BrnoMarsRover/Drilling/code/mainBoardProgram/src/DeepSampler/DeepSampler.cpp

 #include "DeepSampler.h"

// ------------------------------------------------------------------ //
//  Public                                                            //
// ------------------------------------------------------------------ //

DeepSampler::DeepSampler(TwoWire& wire, HardwareSerial& debugSerial):
  _wire(wire),
  _debugSerial(debugSerial),
  _stepperEngine(),
  _drillController(wire, debugSerial, _stepperEngine),
  _deepSampleHolder(wire, debugSerial, _stepperEngine)
{
  
}

bool DeepSampler::begin()
{
  _stepperEngine.init();

  if(_drillController.begin() && _deepSampleHolder.begin())
    return true;
  else
    return false;  
}

void DeepSampler::update()
{
  _drillController.update();
  _deepSampleHolder.update();

  switch(_autoState)
  {
    case AutoState::MANUAL:
    {
      break;
    }

    case AutoState::WAITING_FOR_STORAGE_CLEAR:
    {
      if(!_deepSampleHolder.storageIsMoving())
      {
        if (_deepSampleHolder.storageGetCurrentSlot() == StepperPositioner::StoragePosition::Home)
        {
          if(_drillController.autoDrillToDepth(9, 50, _targetDepthMM ) )
          {
            _autoState = AutoState::DRILLING;
          }
          else
          {
            enterError();
          }
        }
        else
        {
          enterError();
        }
      }
      break;
    }
    
    case AutoState::DRILLING:
    {
      if(_drillController.getAutoState() == DrillController::AutoState::DONE)
      {
        _drillController.setManualControl();
        _autoState = AutoState::MOVE_CARRIAGE_TO_STORE;
      }
      if(_drillController.getAutoState() == DrillController::AutoState::ERROR)
      {
        enterError();
      }
      break;
    }

    case AutoState::MOVE_CARRIAGE_TO_STORE:
    {        
      if(_drillController.spiralDepthBelowSensor() < storingPositionTop)
      {
        if(_drillController.setCarriageSpeedMMps(10))
        {
          _autoState = AutoState::MOVING_CARRIAGE_TO_STORE;
        }
        else
        {
          enterError();
        }
      }
      else if(_drillController.spiralDepthBelowSensor() > storingPositionBottom)
      {
        if(_drillController.setCarriageSpeedMMps(-10))
        {
          _autoState = AutoState::MOVING_CARRIAGE_TO_STORE; 
        }
        else
        {
          enterError();
        }
      }
      else
      {
        _autoState = AutoState::MOVING_CARRIAGE_TO_STORE;
      }
      
      break;
    }

    case AutoState::MOVING_CARRIAGE_TO_STORE:
    {
      if(_drillController.spiralDepthBelowSensor() > storingPositionTop && _drillController.spiralDepthBelowSensor() < storingPositionBottom)
      {
        if(_drillController.setCarriageSpeedMMps(0))
        {
          if(_deepSampleHolder.storageMoveToSlot(_divideSlots[_divideSlotIndex]))
          {
            _autoState = AutoState::MOVING_STORAGE; 
          }
          else
          {
            enterError();
          }
        }
        else
        {
          enterError();
        }
      }
      break;
    }
    
    case AutoState::MOVING_STORAGE:
    {
      if(!_deepSampleHolder.storageIsMoving())
      {
        if(_deepSampleHolder.storageGetCurrentSlot() == _divideSlots[_divideSlotIndex])
        {
          if(_drillController.setSpiralRPM(_storingRPM))
          {
            _storingStartTimeMS = millis();
            _autoState = AutoState::STORING;
          }
          else
          {
            enterError();
          }
        }
        else
        {
          enterError();
        }
      }

      break;
    }
    
    case AutoState::STORING:
    {
      if(millis() - _storingStartTimeMS > _storingDurationMS)
      {
        if(_drillController.setSpiralRPM(0))
        {
          _divideSlotIndex++;
          if(_divideSlotIndex < 3)
          {
            if(_deepSampleHolder.storageMoveToSlot(_divideSlots[_divideSlotIndex]))
            {
              _autoState = AutoState::MOVING_STORAGE;
            }
            else
            {
              enterError();
            }
          }
          else
          {
            if(_deepSampleHolder.startAutoWeighing())
            {
              _autoState = AutoState::WEIGHING;
            }
            else {enterError();}
          }
        }
        else
        {
          enterError();
        }
      }
      break;
    }
    
    case AutoState::WEIGHING:
    {
      if(_deepSampleHolder.getAutoState() == DeepSampleHolder::AutoState::DONE)
      {
        _deepSampleHolder.setManualControl();

        if(_drillController.setCarriageSpeedMMps(-10.0) && _deepSampleHolder.storageMoveToSlot(StepperPositioner::StoragePosition::Home))
        {
          _autoState = AutoState::MOVING_UP;
        }
        else
        {
          enterError();
        }
      }
      if(_deepSampleHolder.getAutoState() == DeepSampleHolder::AutoState::ERROR)
      {
        enterError();
      }
      break;
    }
    
    case AutoState::MOVING_UP:
    {
      if(_drillController.getCarriageDepthMM() < 1.0 && _deepSampleHolder.storageGetCurrentSlot() == StepperPositioner::StoragePosition::Home)
      {
        _autoState = AutoState::DONE;
      }
      break;
    }
  
    case AutoState::DONE:
    {
      break;
    }
    
    case AutoState::ERROR:
    {

      break;
    }
  }
}

// Integrated carriage/spiral motor control
DeepSampler::AutoState DeepSampler::getAutoState() {return _autoState; }
DrillController::AutoState DeepSampler::getDrillControllerState() {return _drillController.getAutoState(); }
DeepSampleHolder::AutoState DeepSampler::getDeepSampleHolderState() {return _deepSampleHolder.getAutoState(); }

bool DeepSampler::setManualControl()
{
  _autoState = AutoState::MANUAL;
  _deepSampleHolder.setManualControl();
  _drillController.setManualControl();
  return true;
}
bool DeepSampler::startDistFromSurfaceMeasure() {return _drillController.startDistFromSurfaceMeasure(); }
float DeepSampler::getDistFromSurfaceMM() {return _drillController.getDistFromSurfaceMM(); }


bool DeepSampler::autoDrillStoreWeigh(float targetDepthMM)
{
  if(_autoState == AutoState::MANUAL && _drillController.isDepthCalibrated())
  {
    if(_deepSampleHolder.storageMoveToSlot(StepperPositioner::StoragePosition::Home))
    {
      _divideSlotIndex = 0;
      _targetDepthMM = targetDepthMM;
      _autoState = AutoState::WAITING_FOR_STORAGE_CLEAR;
      return true;
    }
    else{ return false; }
  }
  else { return false; }
}

bool DeepSampler::autoStoreWeigh()
{
  if(_autoState == AutoState::MANUAL && _drillController.isDepthCalibrated())
  {
    _divideSlotIndex = 0;
    _autoState = AutoState::MOVE_CARRIAGE_TO_STORE;
    return true;
  }
  else {return false;}
}

// Low level carriage/vertical drive control
bool DeepSampler::setCarriageSpeedMMps(float MMps)
{
  return _drillController.setCarriageSpeedMMps(MMps);
}

float DeepSampler::getCarriageSpeedMMps() const { return _drillController.getCarriageSpeedMMps(); }
float DeepSampler::getCarriageDepthMM() const { return _drillController.getCarriageDepthMM(); }
float DeepSampler::getVerticalStepperCurrentA() const { return _drillController.getVerticalStepperCurrentA(); }
bool DeepSampler::currentSensorIsConnected() const {return _drillController.currentSensorIsConnected(); }

// Low level spiral motor control
bool DeepSampler::setSpiralRPM(float rpm) { return _drillController.setSpiralRPM(rpm); }
CubeMarsData DeepSampler::getSpiralMotorData() { return _drillController.getSpiralMotorData(); }

//Storage control
bool DeepSampler::setCalibration0() { return _deepSampleHolder.setCalibration0(); }
bool DeepSampler::setCalibrationX(float weightX) { return _deepSampleHolder.setCalibrationX(weightX); }

bool DeepSampler::getResultReady() { return _deepSampleHolder.getResultReady(); }
WeightResult DeepSampler::getLastWeight() { return _deepSampleHolder.getLastWeight(); }
float DeepSampler::getLastTemp() { return _deepSampleHolder.getLastTemp(); }

bool DeepSampler::requestMeasure() { return _deepSampleHolder.requestMeasure(); }
bool DeepSampler::requestTemp() { return _deepSampleHolder.requestTemp(); }

bool DeepSampler::storageMoveToSlot(StepperPositioner::StoragePosition position)
{
  _deepSampleHolder.storageMoveToSlot(position);
  return true;
}

bool DeepSampler::storageUnlock()
{
  _deepSampleHolder.storageUnlock();
  return true;
}

bool DeepSampler::storageSetHoldMode(bool hold)
{
  _deepSampleHolder.storageSetHoldMode(hold);
  return true;
}

uint16_t DeepSampler::storageGetCurrentAngle()  const {return _deepSampleHolder.storageGetCurrentAngle(); }

// Connection checks
bool DeepSampler::verticalEncoderConnected() {return _drillController.encoderConnected();}
bool DeepSampler::verticalStepperConnected() {return _drillController.stepperConnected();}
bool DeepSampler::spiralMotorConnected() {return _drillController.spiralMotorConnected();}
bool DeepSampler::heightSensorConnected() {return _drillController.heightSensorConnected();}
bool DeepSampler::getAdcConnected() {return _deepSampleHolder.getAdcConnected();}
bool DeepSampler::deepSampleEncoderConnected() {return _deepSampleHolder.storageEncoderConnected(); }
bool DeepSampler::deepSampleStepperConnected() {return _deepSampleHolder.storageStepperConnected(); }

void DeepSampler::enterError()
{
  _drillController.setManualControl();
  _drillController.setCarriageSpeedMMps(0);
  _drillController.setSpiralRPM(0);
  _deepSampleHolder.setManualControl();
  _deepSampleHolder.storageStop();
  _autoState = AutoState::ERROR;
}
