BrnoMarsRover/Drilling/code/pcInterface/protocol.py

"""
protocol.py

Handles building and parsing of UART messages according to the drill protocol spec.

Message format:
  0x02 | length | payload... | checksum | 0x03

Checksum: sum complement of payload bytes (0x100 - (sum(payload) & 0xFF)) & 0xFF

Two-step commands (trigger then poll):
  WEIGH_DEEP        -> GET_WEIGHT_DEEP
  WEIGH_SURFACE     -> GET_WEIGHT_SURFACE
  START_DEV_CHECK   -> GET_DEVICE_STATUS
  MEASURE_HEIGHT    -> GET_HEIGHT
"""

import struct

# --- Message framing bytes ---
STX = 0x02
ETX = 0x03

# --- Command codes ---
CMD_RESTART            = 0x01
CMD_STATE              = 0x02
CMD_CALIBRATE_HEIGHT   = 0x03
CMD_START_DEV_CHECK    = 0x04
CMD_GET_DEVICE_STATUS  = 0x05
CMD_DRILL_SPEED        = 0x20
CMD_VERTICAL_SPEED     = 0x21
CMD_STORAGE_POSITION   = 0x22
CMD_MEASURE_HEIGHT     = 0x23
CMD_GET_HEIGHT         = 0x24
CMD_WEIGH_DEEP         = 0x40
CMD_WEIGH_SURFACE      = 0x41
CMD_GET_WEIGHT_DEEP    = 0x42
CMD_GET_WEIGHT_SURFACE = 0x43
CMD_CALIBRATE_0_DEEP   = 0x44
CMD_CALIBRATE_X_DEEP   = 0x45
CMD_CALIBRATE_0_SURFACE= 0x46
CMD_CALIBRATE_X_SURFACE= 0x47
CMD_ROCK_OPEN          = 0x50
CMD_ROCK_CLOSE         = 0x51
CMD_SAND_OPEN          = 0x52
CMD_SAND_CLOSE         = 0x53
CMD_SET_HOLD_MODE      = 0x54
CMD_CLEAR_HOLD_MODE    = 0x55
CMD_STOP_AUTO          = 0x60
CMD_DRILL_AUTO         = 0x61
CMD_STORE_AUTO         = 0x62


# --- Autonomy state codes ---
# Three independent state machines, each reported as its own uint8 in the
# STATE response. Codes and meanings per protocol spec.

DEEP_SAMPLER_STATE_CODES = {
    0x00: "MANUAL",
    0x01: "WAITING_FOR_STORAGE_CLEAR",
    0x02: "DRILLING",
    0x03: "MOVE_CARRIAGE_TO_STORE",
    0x04: "MOVING_CARRIAGE_TO_STORE",
    0x05: "MOVING_STORAGE",
    0x06: "STORING",
    0x07: "WEIGHING",
    0x08: "MOVING_UP",
    0xFE: "DONE",
    0xFF: "ERROR",
}

DRILL_CONTROLLER_STATE_CODES = {
    0x00: "MANUAL",
    0x01: "WAITING_FOR_HEIGHT",
    0x02: "MOVING_DOWN",
    0x03: "DRILLING",
    0xFE: "DONE",
    0xFF: "ERROR",
}

DEEP_SAMPLE_HOLDER_STATE_CODES = {
    0x00: "MANUAL",
    0x01: "STORAGE_MOVING",
    0x02: "WAITING_FOR_SETTLE",
    0x03: "WEIGHING",
    0xFE: "DONE",
    0xFF: "ERROR",
}

# --- Device status bit order (LSB first) ---
DEVICE_NAMES = [
    "Vertical drive stepper driver",   # bit 0
    "Vertical drive encoder",          # bit 1
    "Vertical drive current sensor",   # bit 2
    "Spiral motor",                    # bit 3
    "Height sensor",                   # bit 4
    "Deep storage stepper driver",     # bit 5
    "Deep storage encoder",            # bit 6
    "Deep sample ADC",                 # bit 7
    "Surface sample ADC",              # bit 8
]


def checksum(payload: bytes) -> int:
    """Sum complement checksum over payload bytes."""
    return (0x100 - (sum(payload) & 0xFF)) & 0xFF


def build_message(payload: bytes) -> bytes:
    """Wrap a payload in the full message frame."""
    cs = checksum(payload)
    return bytes([STX, len(payload)]) + payload + bytes([cs, ETX])


def build_command(code: int, argument: bytes = b"") -> bytes:
    """Build a complete framed message for a given command code and optional argument."""
    payload = bytes([code]) + argument
    return build_message(payload)


# --- Convenience command builders ---

def cmd_restart():
    return build_command(CMD_RESTART)

def cmd_state():
    return build_command(CMD_STATE)

def cmd_drill_auto(depth_cm: int):
    return build_command(CMD_DRILL_AUTO, struct.pack("B", depth_cm))

def cmd_stop_auto():
    return build_command(CMD_STOP_AUTO)

def cmd_calibrate_height():
    return build_command(CMD_CALIBRATE_HEIGHT)

def cmd_start_dev_check():
    return build_command(CMD_START_DEV_CHECK)

def cmd_get_device_status():
    return build_command(CMD_GET_DEVICE_STATUS)

def cmd_store_auto():
    return build_command(CMD_STORE_AUTO)

def cmd_drill_speed(rpm: int):
    return build_command(CMD_DRILL_SPEED, struct.pack(">h", rpm))

def cmd_vertical_speed(mm_per_s: float):
    # convert float mm/s to int8 (units of 0.1 mm/s)
    raw = int(round(mm_per_s * 10))
    return build_command(CMD_VERTICAL_SPEED, struct.pack("b", raw))

def cmd_storage_position(position: int):
    return build_command(CMD_STORAGE_POSITION, struct.pack("B", position))

def cmd_measure_height():
    return build_command(CMD_MEASURE_HEIGHT)

def cmd_get_height():
    return build_command(CMD_GET_HEIGHT)

def cmd_weigh_deep():
    return build_command(CMD_WEIGH_DEEP)

def cmd_weigh_surface():
    return build_command(CMD_WEIGH_SURFACE)

def cmd_get_weight_deep():
    return build_command(CMD_GET_WEIGHT_DEEP)

def cmd_get_weight_surface():
    return build_command(CMD_GET_WEIGHT_SURFACE)

def cmd_calibrate_0_deep():
    return build_command(CMD_CALIBRATE_0_DEEP)

def cmd_calibrate_x_deep(weight_g: float):
    return build_command(CMD_CALIBRATE_X_DEEP, struct.pack(">f", weight_g))

def cmd_calibrate_0_surface():
    return build_command(CMD_CALIBRATE_0_SURFACE)

def cmd_calibrate_x_surface(weight_g: float):
    return build_command(CMD_CALIBRATE_X_SURFACE, struct.pack(">f", weight_g))

def cmd_set_hold_mode():
    return build_command(CMD_SET_HOLD_MODE)

def cmd_clear_hold_mode():
    return build_command(CMD_CLEAR_HOLD_MODE)

def cmd_rock_open():
    return build_command(CMD_ROCK_OPEN)

def cmd_rock_close():
    return build_command(CMD_ROCK_CLOSE)

def cmd_sand_open():
    return build_command(CMD_SAND_OPEN)

def cmd_sand_close():
    return build_command(CMD_SAND_CLOSE)


# --- Response parsing ---

def parse_response(data: bytes):
    """
    Parse a complete raw message (including framing bytes).
    Returns a dict with parsed fields, or None if the message is invalid.

    Possible keys in the returned dict:
      'code'          : int   — the echoed command code (or 0 for NACK)
      'nack'          : bool  — True if the drill refused the command
      'state'         : dict  — present if code == CMD_STATE. Includes
                                 separate deep_sampler_state,
                                 drill_controller_state, and
                                 deep_sample_holder_state fields (each
                                 with a matching *_str name).
      'weight'        : float — present if code == CMD_GET_WEIGHT_DEEP/SURFACE
      'adc_raw'       : int   — raw ADC value, present alongside 'weight'
      'height_mm'     : int   — present if code == CMD_GET_HEIGHT
      'device_status' : list  — present if code == CMD_GET_DEVICE_STATUS
    """
    if len(data) < 5:
        return None
    if data[0] != STX or data[-1] != ETX:
        return None

    payload_length = data[1]
    payload = data[2 : 2 + payload_length]
    received_checksum = data[2 + payload_length]

    if len(payload) != payload_length:
        return None
    if checksum(payload) != received_checksum:
        return None

    code = payload[0]

    if code == 0x00:
        return {"code": 0, "nack": True}

    result = {"code": code, "nack": False}

    if code == CMD_STATE and len(payload) >= 19:
        # int16 height_mm, int8 vert_speed, uint8 stepper_current,
        # int16 rpm, int16 motor_winding_current, int16 motor_current_draw,
        # int16 motor_torque, uint8 temp, uint16 tray_angle,
        # uint8 deep_sampler_state, uint8 drill_controller_state,
        # uint8 deep_sample_holder_state
        (height, vert_speed, current, rpm,
         motor_winding_current, motor_current_draw, motor_torque,
         temp, tray_angle, deep_sampler_state, drill_controller_state,
         deep_sample_holder_state) = \
            struct.unpack_from(">hbBhhhhBHBBB", payload, 1)
        result["state"] = {
            "height_mm":               height,
            "vert_speed":              vert_speed / 10.0,
            "current_a":               current / 100.0,
            "rpm":                     rpm,
            "motor_winding_current_a": motor_winding_current / 100.0,
            "motor_current_draw_a":    motor_current_draw / 100.0,
            "motor_torque_nm":         motor_torque / 100.0,
            "temp_c":                  temp,
            "tray_angle":              tray_angle,
            "deep_sampler_state":      deep_sampler_state,
            "deep_sampler_state_str": DEEP_SAMPLER_STATE_CODES.get(
                deep_sampler_state, f"Unknown (0x{deep_sampler_state:02X})"),
            "drill_controller_state":  drill_controller_state,
            "drill_controller_state_str": DRILL_CONTROLLER_STATE_CODES.get(
                drill_controller_state, f"Unknown (0x{drill_controller_state:02X})"),
            "deep_sample_holder_state": deep_sample_holder_state,
            "deep_sample_holder_state_str": DEEP_SAMPLE_HOLDER_STATE_CODES.get(
                deep_sample_holder_state, f"Unknown (0x{deep_sample_holder_state:02X})"),
        }

    elif code in (CMD_GET_WEIGHT_DEEP, CMD_GET_WEIGHT_SURFACE) and len(payload) >= 9:
        weight, adc_raw = struct.unpack_from(">fI", payload, 1)
        result["weight"]  = weight
        result["adc_raw"] = adc_raw

    elif code == CMD_GET_HEIGHT and len(payload) >= 3:
        result["height_mm"] = struct.unpack_from(">H", payload, 1)[0]

    elif code == CMD_GET_DEVICE_STATUS and len(payload) >= 3:
        status_bits = struct.unpack_from(">H", payload, 1)[0]
        devices = []
        for i, name in enumerate(DEVICE_NAMES):
            devices.append({
                "name": name,
                "ok":   bool(status_bits & (1 << i)),
            })
        result["device_status"] = devices

    return result
