BrnoMarsRover/Drilling/code/pcInterface/gui.py

"""
gui.py

Tkinter GUI for the drilling HMI.
All communication goes through the CommWorker — the GUI never touches the
serial port or UDP socket directly. CommWorker supports two transports,
switchable from the Connection bar: direct USB serial to the ESP32, or a
localhost UDP link to the main rover communication app.

Layout (4 columns, 2 content rows):
  Col 0: Drill status + Manual controls
  Col 1 row 1: Auto drilling + Height measurement
  Col 1 row 2: Sample handling
  Col 2 row 1: Device status
  Col 2 row 2: Calibration
  Col 3 rows 1-2: Log
"""

import tkinter as tk
from tkinter import ttk, messagebox
import serial.tools.list_ports
import protocol
import time

POLL_INTERVAL_MS       = 100
STATE_POLL_INTERVAL_MS = 500

# Localhost UDP ports, per communicationProtocol.md:
# this app sends to the main rover app on 5610 and receives replies on 5611.
DEFAULT_UDP_SEND_PORT   = 5610
DEFAULT_UDP_LISTEN_PORT = 5611


class App(tk.Tk):
    def __init__(self, worker):
        super().__init__()
        self.worker = worker
        self.title("Drilling HMI")
        self.resizable(True, True)

        self._build_connection_bar()
        self._build_columns()
        self._build_status_panel()
        self._build_manual_controls()
        self._build_height_panel()
        self._build_autonomy_controls()
        self._build_sample_controls()
        self._build_device_status_panel()
        self._build_weight_panel()
        self._build_calibration_panel()
        self._build_log()

        self._configure_resizing()

        self._poll_rx()
        self._poll_state()

    def _build_columns(self):
        """
        One container per column. Panels are packed vertically inside their
        column, so a tall panel in one column no longer forces gaps between
        the panels of its neighbours (which a shared grid row would).
        """
        self.columns = []
        for i in range(4):
            container = ttk.Frame(self)
            container.grid(row=1, column=i, sticky="nsew")
            self.columns.append(container)

    def _configure_resizing(self):
        """
        Let the window be resized. The log column takes the extra width and
        the two content rows share the extra height; the fixed-content
        columns keep their natural size. The minimum size is locked to the
        laid-out size so nothing can be clipped by shrinking the window.
        """
        # Column 3 (log) absorbs horizontal growth; the other columns hold
        # fixed-size controls and keep their natural width.
        self.columnconfigure(3, weight=1)
        # The single content row absorbs vertical growth;
        # row 0 (connection bar) stays fixed.
        self.rowconfigure(1, weight=1)

        self.update_idletasks()
        self.minsize(self.winfo_reqwidth(), self.winfo_reqheight())

    # ------------------------------------------------------------------ #
    #  Connection bar                                                      #
    # ------------------------------------------------------------------ #

    def _build_connection_bar(self):
        frame = ttk.LabelFrame(self, text="Connection")
        frame.grid(row=0, column=0, columnspan=4, padx=8, pady=6, sticky="ew")

        # --- Transport mode selector ---
        ttk.Label(frame, text="Mode:").grid(row=0, column=0, padx=4, pady=4)
        self.conn_mode_var = tk.StringVar(value="serial")
        self.serial_radio = ttk.Radiobutton(
            frame, text="USB Serial", variable=self.conn_mode_var,
            value="serial", command=self._on_mode_change)
        self.serial_radio.grid(row=0, column=1, padx=(4, 0), pady=4, sticky="w")
        self.udp_radio = ttk.Radiobutton(
            frame, text="UDP (localhost)", variable=self.conn_mode_var,
            value="udp", command=self._on_mode_change)
        self.udp_radio.grid(row=0, column=2, padx=(4, 12), pady=4, sticky="w")

        # --- Serial-specific controls (shown when Mode == USB Serial) ---
        self.serial_frame = ttk.Frame(frame)
        self.serial_frame.grid(row=0, column=3, padx=4, pady=4, sticky="w")
        ttk.Label(self.serial_frame, text="COM port:").pack(side="left")
        self.port_var = tk.StringVar()
        self.port_combo = ttk.Combobox(
            self.serial_frame, textvariable=self.port_var, width=12, state="readonly")
        self.port_combo.pack(side="left", padx=4)
        self.refresh_btn = ttk.Button(self.serial_frame, text="Refresh", command=self._refresh_ports)
        self.refresh_btn.pack(side="left")

        # --- UDP-specific controls (shown when Mode == UDP) ---
        self.udp_frame = ttk.Frame(frame)
        self.udp_frame.grid(row=0, column=3, padx=4, pady=4, sticky="w")
        ttk.Label(self.udp_frame, text="Listen port (from main app):").pack(side="left")
        self.udp_local_port_var = tk.StringVar(value=str(DEFAULT_UDP_LISTEN_PORT))
        ttk.Entry(self.udp_frame, textvariable=self.udp_local_port_var, width=6).pack(
            side="left", padx=(4, 12))
        ttk.Label(self.udp_frame, text="Send port (to main app):").pack(side="left")
        self.udp_remote_port_var = tk.StringVar(value=str(DEFAULT_UDP_SEND_PORT))
        ttk.Entry(self.udp_frame, textvariable=self.udp_remote_port_var, width=6).pack(
            side="left", padx=4)

        self.connect_btn = ttk.Button(frame, text="Connect", command=self._toggle_connection)
        self.connect_btn.grid(row=0, column=4, padx=4)
        self.conn_status = ttk.Label(frame, text="Disconnected", foreground="red")
        self.conn_status.grid(row=0, column=5, padx=8)

        self._refresh_ports()
        self._on_mode_change()

    def _on_mode_change(self):
        """Show the controls relevant to the selected transport mode."""
        if self.conn_mode_var.get() == "serial":
            self.udp_frame.grid_remove()
            self.serial_frame.grid()
        else:
            self.serial_frame.grid_remove()
            self.udp_frame.grid()

    def _set_mode_controls_enabled(self, enabled: bool):
        """Lock the mode switch and its fields while connected."""
        state = "normal" if enabled else "disabled"
        combo_state = "readonly" if enabled else "disabled"
        self.serial_radio.config(state=state)
        self.udp_radio.config(state=state)
        self.port_combo.config(state=combo_state)
        self.refresh_btn.config(state=state)
        for child in self.udp_frame.winfo_children():
            if isinstance(child, ttk.Entry):
                child.config(state=state)

    def _refresh_ports(self):
        ports = [p.device for p in serial.tools.list_ports.comports()]
        self.port_combo["values"] = ports
        if ports:
            self.port_combo.current(0)

    def _toggle_connection(self):
        if self.worker.is_connected():
            self.worker.disconnect()
            self.connect_btn.config(text="Connect")
            self.conn_status.config(text="Disconnected", foreground="red")
            self._set_mode_controls_enabled(True)
            self._log("Disconnected.")
            return

        mode = self.conn_mode_var.get()

        if mode == "serial":
            port = self.port_var.get()
            if not port:
                messagebox.showerror("Error", "No COM port selected.")
                return
            ok = self.worker.connect_serial(port)
            description = port
        else:
            try:
                local_port = int(self.udp_local_port_var.get())
                remote_port = int(self.udp_remote_port_var.get())
            except ValueError:
                messagebox.showerror("Error", "UDP ports must be numbers.")
                return
            if not (0 < local_port <= 65535 and 0 < remote_port <= 65535):
                messagebox.showerror("Error", "UDP ports must be between 1 and 65535.")
                return
            if local_port == remote_port:
                messagebox.showerror("Error", "Listen port and send port must be different.")
                return
            ok = self.worker.connect_udp(local_port, remote_port)
            description = f"UDP — listen {local_port} / send {remote_port}"

        if ok:
            self.connect_btn.config(text="Disconnect")
            self.conn_status.config(text=f"Connected ({description})", foreground="green")
            self._set_mode_controls_enabled(False)
            self._log(f"Connected: {description}.")
        else:
            self._log(f"Failed to connect: {description}.")

    # ------------------------------------------------------------------ #
    #  Status panel (STATE response)  — column 0                          #
    # ------------------------------------------------------------------ #

    def _build_status_panel(self):
        frame = ttk.LabelFrame(self.columns[0], text="Drill status  (auto-refreshed)")
        frame.pack(fill="x", padx=8, pady=6)

        # Numeric readouts — a narrow fixed width is enough for every value
        # these ever hold, and it keeps the left column compact.
        labels = [
            ("Carriage depth",         "carriage_depth_var",  "mm"),
            ("Depth under rover",      "depth_under_rover_var","mm"),
            ("Depth under surface",    "depth_under_surface_var","mm"),
            ("Vertical speed",         "vert_speed_actual_var","mm/s"),
            ("Stepper current",        "current_var",         "A"),
            ("Motor speed",            "rpm_var",             "RPM"),
            ("Motor winding current",  "motor_winding_current_var", "A"),
            ("Motor current draw",     "motor_current_draw_var",    "A"),
            ("Motor torque",           "motor_torque_var",    "Nm"),
            ("Motor temp",             "temp_var",            "°C"),
            ("Tray angle",             "tray_var",            "°"),
        ]

        for i, (label, attr, unit) in enumerate(labels):
            ttk.Label(frame, text=label + ":").grid(row=i, column=0, sticky="w", padx=6, pady=2)
            var = tk.StringVar(value="—")
            setattr(self, attr, var)
            ttk.Label(frame, textvariable=var, width=10, anchor="w").grid(
                row=i, column=1, sticky="w", padx=4)
            if unit:
                ttk.Label(frame, text=unit).grid(row=i, column=2, sticky="w", padx=(0, 6))

        ttk.Separator(frame, orient="horizontal").grid(
            row=len(labels), column=0, columnspan=3, sticky="ew", pady=4)

        # State names are long (e.g. MOVING_CARRIAGE_TO_STORE). Wrapping them
        # instead of reserving a wide column keeps the text fully readable
        # without stretching the panel.
        states = [
            ("DeepSampler",      "deep_sampler_state_var"),
            ("DrillController",  "drill_controller_state_var"),
            ("DeepSampleHolder", "deep_sample_holder_state_var"),
        ]
        for j, (label, attr) in enumerate(states):
            row = len(labels) + 1 + j
            ttk.Label(frame, text=label + ":").grid(row=row, column=0, sticky="nw", padx=6, pady=2)
            var = tk.StringVar(value="—")
            setattr(self, attr, var)
            ttk.Label(frame, textvariable=var, wraplength=110,
                      justify="left", anchor="w").grid(
                row=row, column=1, columnspan=2, sticky="w", padx=4)

    # ------------------------------------------------------------------ #
    #  Manual controls — column 0                                          #
    # ------------------------------------------------------------------ #

    def _build_manual_controls(self):
        frame = ttk.LabelFrame(self.columns[0], text="Manual controls")
        frame.pack(fill="x", padx=8, pady=6)

        ttk.Label(frame, text="Drill speed (RPM):").grid(row=0, column=0, sticky="w", padx=6, pady=3)
        self.drill_speed_var = tk.StringVar(value="0")
        ttk.Entry(frame, textvariable=self.drill_speed_var, width=8).grid(row=0, column=1, padx=4)
        ttk.Button(frame, text="Set", width=4, command=self._set_drill_speed).grid(
            row=0, column=2, padx=4)
        ttk.Button(frame, text="Stop", width=5, command=self._stop_drill_speed).grid(
            row=0, column=3, padx=(0, 6))

        ttk.Label(frame, text="Vertical speed (mm/s):").grid(row=1, column=0, sticky="w", padx=6, pady=3)
        self.vert_speed_request_var = tk.StringVar(value="0")
        ttk.Entry(frame, textvariable=self.vert_speed_request_var, width=8).grid(row=1, column=1, padx=4)
        ttk.Button(frame, text="Set", width=4, command=self._set_vertical_speed).grid(
            row=1, column=2, padx=4)
        ttk.Button(frame, text="Stop", width=5, command=self._stop_vertical_speed).grid(
            row=1, column=3, padx=(0, 6))

        ttk.Label(frame, text="Storage position:").grid(row=2, column=0, sticky="w", padx=6, pady=3)
        self.storage_pos_var = tk.StringVar(value="0")
        ttk.Entry(frame, textvariable=self.storage_pos_var, width=8).grid(row=2, column=1, padx=4)
        ttk.Button(frame, text="Set", width=4, command=self._set_storage_position).grid(
            row=2, column=2, padx=4)

        ttk.Separator(frame, orient="horizontal").grid(
            row=3, column=0, columnspan=4, sticky="ew", pady=6)

        ttk.Button(frame, text="Calibrate carriage depth", command=self._calibrate_height).grid(
            row=4, column=0, columnspan=4, sticky="ew", padx=6, pady=2)
        ttk.Button(frame, text="RESTART", command=self._restart).grid(
            row=5, column=0, columnspan=4, sticky="ew", padx=6, pady=2)

    # ------------------------------------------------------------------ #
    #  Automatic drilling — column 1                                       #
    # ------------------------------------------------------------------ #

    def _build_height_panel(self):
        frame = ttk.LabelFrame(self.columns[1], text="Height measurement")
        frame.pack(fill="x", padx=8, pady=6)

        ttk.Label(frame, text="Height above ground:").grid(
            row=0, column=0, sticky="w", padx=6, pady=2)
        self.height_above_ground_var = tk.StringVar(value="—")
        ttk.Label(frame, textvariable=self.height_above_ground_var, width=8, anchor="w").grid(
            row=0, column=1, sticky="w", padx=4)
        ttk.Label(frame, text="mm").grid(row=0, column=2, sticky="w", padx=(0, 6))

        ttk.Button(frame, text="Measure height above ground", command=self._measure_height).grid(
            row=1, column=0, columnspan=3, sticky="ew", padx=6, pady=2)
        ttk.Button(frame, text="Get height above ground", command=self._get_height).grid(
            row=2, column=0, columnspan=3, sticky="ew", padx=6, pady=(2, 6))

    # ------------------------------------------------------------------ #
    #  Autonomy — column 1                                                 #
    # ------------------------------------------------------------------ #

    def _build_autonomy_controls(self):
        frame = ttk.LabelFrame(self.columns[1], text="Autonomy")
        frame.pack(fill="x", padx=8, pady=6)

        ttk.Label(frame, text="Target depth (cm):").grid(row=0, column=0, sticky="w", padx=6, pady=3)
        self.drill_depth_var = tk.StringVar(value="10")
        ttk.Entry(frame, textvariable=self.drill_depth_var, width=8).grid(
            row=0, column=1, sticky="w", padx=4)

        ttk.Button(frame, text="Start auto drill", command=self._drill_auto).grid(
            row=1, column=0, columnspan=2, sticky="ew", padx=6, pady=4)
        ttk.Button(frame, text="Start auto store", command=self._store_auto).grid(
            row=2, column=0, columnspan=2, sticky="ew", padx=6, pady=2)

        ttk.Separator(frame, orient="horizontal").grid(
            row=3, column=0, columnspan=2, sticky="ew", pady=6)

        ttk.Button(frame, text="Stop auto", command=self._stop_auto).grid(
            row=4, column=0, columnspan=2, sticky="ew", padx=6, pady=(2, 6))

    # ------------------------------------------------------------------ #
    #  Sample handling — column 1                                          #
    # ------------------------------------------------------------------ #

    def _build_sample_controls(self):
        frame = ttk.LabelFrame(self.columns[1], text="Sample handling")
        frame.pack(fill="x", padx=8, pady=6)

        # Two columns: the action and its matching counterpart side by side.
        rows = [
            ("Weigh deep",    self._weigh_deep,    "Get deep",    self._get_weight_deep),
            ("Weigh surface", self._weigh_surface, "Get surface", self._get_weight_surface),
            ("Rock open",     self._rock_open,     "Rock close",  self._rock_close),
            ("Sand open",     self._sand_open,     "Sand close",  self._sand_close),
            ("Set hold",      self._set_hold_mode, "Clear hold",  self._clear_hold_mode),
        ]
        for i, (left_label, left_cmd, right_label, right_cmd) in enumerate(rows):
            ttk.Button(frame, text=left_label, command=left_cmd).grid(
                row=i, column=0, sticky="ew", padx=(6, 2), pady=2)
            ttk.Button(frame, text=right_label, command=right_cmd).grid(
                row=i, column=1, sticky="ew", padx=(2, 6), pady=2)

        frame.columnconfigure(0, weight=1, uniform="sample")
        frame.columnconfigure(1, weight=1, uniform="sample")



    # ------------------------------------------------------------------ #
    #  Device status — column 2, row 1                                     #
    # ------------------------------------------------------------------ #

    def _build_device_status_panel(self):
        frame = ttk.LabelFrame(self.columns[2], text="Device status")
        frame.pack(fill="x", padx=8, pady=6)

        ttk.Button(frame, text="Check devices", command=self._start_dev_check).grid(
            row=0, column=0, columnspan=2, sticky="ew", padx=6, pady=4)
        ttk.Button(frame, text="Get device status", command=self._get_device_status).grid(
            row=1, column=0, columnspan=2, sticky="ew", padx=6, pady=2)

        ttk.Separator(frame, orient="horizontal").grid(
            row=2, column=0, columnspan=2, sticky="ew", pady=6)

        self._device_indicators = []
        for i, name in enumerate(protocol.DEVICE_NAMES):
            indicator = tk.Label(frame, text="●", foreground="grey", font=("TkDefaultFont", 12))
            indicator.grid(row=3+i, column=0, padx=(6, 2), pady=1)
            ttk.Label(frame, text=name, anchor="w").grid(row=3+i, column=1, sticky="w", padx=(0, 6))
            self._device_indicators.append(indicator)

    def _update_device_indicators(self, devices: list):
        for i, device in enumerate(devices):
            color = "green" if device["ok"] else "red"
            self._device_indicators[i].config(foreground=color)

    # ------------------------------------------------------------------ #
    #  Calibration — column 3, row 2                                       #
    # ------------------------------------------------------------------ #

    def _build_weight_panel(self):
        frame = ttk.LabelFrame(self.columns[2], text="Weight")
        frame.pack(fill="x", padx=8, pady=6)

        weights = [
            ("Weight (deep)",    "weight_deep_var"),
            ("Weight (surface)", "weight_surface_var"),
        ]
        for i, (label, attr) in enumerate(weights):
            ttk.Label(frame, text=label + ":").grid(row=i, column=0, sticky="w", padx=6, pady=2)
            var = tk.StringVar(value="—")
            setattr(self, attr, var)
            ttk.Label(frame, textvariable=var, width=10, anchor="w").grid(
                row=i, column=1, sticky="w", padx=4)
            ttk.Label(frame, text="g").grid(row=i, column=2, sticky="w", padx=(0, 6))

    # ------------------------------------------------------------------ #
    #  Calibration — column 2                                              #
    # ------------------------------------------------------------------ #

    def _build_calibration_panel(self):
        frame = ttk.LabelFrame(self.columns[2], text="Calibration")
        frame.pack(fill="x", padx=8, pady=6)

        ttk.Label(frame, text="Calibration weight (g):").grid(
            row=0, column=0, sticky="w", padx=6, pady=2)
        self.calib_weight_var = tk.StringVar(value="100.0")
        ttk.Entry(frame, textvariable=self.calib_weight_var, width=8).grid(
            row=0, column=1, padx=4)

        calib_buttons = [
            ("Cal 0g — deep",    self._calibrate_0_deep),
            ("Cal Xg — deep",    self._calibrate_x_deep),
            ("Cal 0g — surface", self._calibrate_0_surface),
            ("Cal Xg — surface", self._calibrate_x_surface),
        ]
        for i, (label, cmd) in enumerate(calib_buttons):
            ttk.Button(frame, text=label, command=cmd).grid(
                row=i+1, column=0, columnspan=2, sticky="ew", padx=6, pady=2)

    # ------------------------------------------------------------------ #
    #  Log — column 3, row 1                                               #
    # ------------------------------------------------------------------ #

    def _build_log(self):
        frame = ttk.LabelFrame(self.columns[3], text="Log")
        frame.pack(fill="both", expand=True, padx=8, pady=6)

        self.auto_scroll_var = tk.BooleanVar(value=True)
        ttk.Checkbutton(frame, text="Auto-scroll", variable=self.auto_scroll_var).grid(
            row=0, column=0, columnspan=2, sticky="w", padx=4, pady=(4, 0))

        # Narrow minimum — the log column absorbs any extra window width,
        # so this only sets how small it may be squeezed, not how it looks.
        self.log_text = tk.Text(frame, height=30, width=28, state="disabled",
                                wrap="word", font=("Courier New", 9))
        self.log_text.grid(row=1, column=0, sticky="nsew", padx=4, pady=4)
        scrollbar = ttk.Scrollbar(frame, command=self.log_text.yview)
        scrollbar.grid(row=1, column=1, sticky="ns")
        self.log_text.config(yscrollcommand=scrollbar.set)
        frame.rowconfigure(1, weight=1)
        frame.columnconfigure(0, weight=1)

    def _log(self, message: str):
        timestamp = time.strftime("%H:%M:%S")
        self.log_text.config(state="normal")
        self.log_text.insert("end", "[" + timestamp + "] " + message + "\n")
        # self.log_text.insert("end", message + "\n")
        if self.auto_scroll_var.get():
            self.log_text.see("end")
        self.log_text.config(state="disabled")

    # ------------------------------------------------------------------ #
    #  Computed depth helpers                                              #
    # ------------------------------------------------------------------ #

    # Constants from protocol spec (mm)
    _CARRIAGE_TOP_TO_SPIRAL_TIP_MM = 720
    _LIN_AXIS_ZERO_TO_SENSOR_MM    = 775

    # Last known values — None until first data arrives
    _last_carriage_depth_mm      = None
    _last_height_above_ground_mm = None

    def _update_computed_depths(self):
        if self._last_carriage_depth_mm is None:
            return

        offset = self._last_carriage_depth_mm + self._CARRIAGE_TOP_TO_SPIRAL_TIP_MM - self._LIN_AXIS_ZERO_TO_SENSOR_MM
        self.depth_under_rover_var.set(str(offset))

        if self._last_height_above_ground_mm is not None:
            under_surface = offset - self._last_height_above_ground_mm
            self.depth_under_surface_var.set(str(under_surface))
        else:
            self.depth_under_surface_var.set("— no height")

    # ------------------------------------------------------------------ #
    #  Polling loops                                                       #
    # ------------------------------------------------------------------ #

    def _poll_rx(self):
        while not self.worker.rx_queue.empty():
            try:
                msg = self.worker.rx_queue.get_nowait()
                self._handle_message(msg)
            except Exception:
                pass
        self.after(POLL_INTERVAL_MS, self._poll_rx)

    def _poll_state(self):
        if self.worker.is_connected():
            self.worker.send(protocol.cmd_state())
        self.after(STATE_POLL_INTERVAL_MS, self._poll_state)

    def _handle_message(self, msg: dict):
        if "debug" in msg:
            self._log(f"[ESP] {msg['debug']}")
            return

        if "error" in msg:
            self._log(f"ERROR: {msg['error']}")
            return

        if msg.get("nack"):
            self._log("NACK — drill refused the command.")
            return

        code = msg.get("code")

        if code == protocol.CMD_STATE and "state" in msg:
            s = msg["state"]
            self._last_carriage_depth_mm = s["height_mm"]
            self.carriage_depth_var.set(str(s["height_mm"]))
            self._update_computed_depths()
            self.vert_speed_actual_var.set(f"{s['vert_speed']:.1f}")
            self.current_var.set(f"{s['current_a']:.2f}")
            self.rpm_var.set(str(s["rpm"]))
            self.motor_winding_current_var.set(f"{s['motor_winding_current_a']:.2f}")
            self.motor_current_draw_var.set(f"{s['motor_current_draw_a']:.2f}")
            self.motor_torque_var.set(f"{s['motor_torque_nm']:.2f}")
            self.temp_var.set(str(s["temp_c"]))
            self.tray_var.set(str(s["tray_angle"]))
            self.deep_sampler_state_var.set(s["deep_sampler_state_str"])
            self.drill_controller_state_var.set(s["drill_controller_state_str"])
            self.deep_sample_holder_state_var.set(s["deep_sample_holder_state_str"])

        elif code == protocol.CMD_GET_HEIGHT and "height_mm" in msg:
            self._last_height_above_ground_mm = msg["height_mm"]
            self.height_above_ground_var.set(str(msg["height_mm"]))
            self._update_computed_depths()
            self._log(f"Height above ground: {msg['height_mm']} mm")

        elif code == protocol.CMD_GET_WEIGHT_DEEP and "weight" in msg:
            self.weight_deep_var.set(f"{msg['weight']:.2f}")
            self._log(f"Deep sample weight: {msg['weight']:.2f} g  (raw ADC: {msg['adc_raw']})")

        elif code == protocol.CMD_GET_WEIGHT_SURFACE and "weight" in msg:
            self.weight_surface_var.set(f"{msg['weight']:.2f}")
            self._log(f"Surface sample weight: {msg['weight']:.2f} g  (raw ADC: {msg['adc_raw']})")

        elif code == protocol.CMD_GET_DEVICE_STATUS and "device_status" in msg:
            self._update_device_indicators(msg["device_status"])
            failed = [d["name"] for d in msg["device_status"] if not d["ok"]]
            if failed:
                self._log(f"Device check — failed: {', '.join(failed)}")
            else:
                self._log("Device check — all devices OK.")

        else:
            self._log(f"ACK: command 0x{code:02X}")

    # ------------------------------------------------------------------ #
    #  Command handlers                                                    #
    # ------------------------------------------------------------------ #

    def _send(self, raw: bytes, description: str):
        if not self.worker.is_connected():
            self._log("Not connected.")
            return
        self.worker.send(raw)
        self._log(f"Sent: {description}")

    def _restart(self):
        if messagebox.askyesno("Confirm", "Restart the drill controller?"):
            self._send(protocol.cmd_restart(), "RESTART")

    def _calibrate_height(self):
        self._send(protocol.cmd_calibrate_height(), "CALIBRATE HEIGHT")

    def _measure_height(self):
        self._send(protocol.cmd_measure_height(), "MEASURE HEIGHT")

    def _get_height(self):
        self._send(protocol.cmd_get_height(), "GET HEIGHT")

    def _start_dev_check(self):
        self._send(protocol.cmd_start_dev_check(), "START DEVICE CHECK")

    def _get_device_status(self):
        self._send(protocol.cmd_get_device_status(), "GET DEVICE STATUS")

    def _set_drill_speed(self):
        try:
            rpm = int(self.drill_speed_var.get())
            self._send(protocol.cmd_drill_speed(rpm), f"DRILL SPEED {rpm} RPM")
        except ValueError:
            self._log("Invalid RPM value.")

    def _set_vertical_speed(self):
        try:
            mm_s = float(self.vert_speed_request_var.get())
            if not (-12.8 <= mm_s <= 12.7):
                self._log("Vertical speed must be between -12.8 and 12.7 mm/s.")
                return
            self._send(protocol.cmd_vertical_speed(mm_s), f"VERTICAL SPEED {mm_s} mm/s")
        except ValueError:
            self._log("Invalid speed value.")

    def _stop_drill_speed(self):
        """Send drill speed 0. The entry keeps its value so Set can resume it."""
        self._send(protocol.cmd_drill_speed(0), "DRILL SPEED 0 RPM")

    def _stop_vertical_speed(self):
        """Send vertical speed 0. The entry keeps its value so Set can resume it."""
        self._send(protocol.cmd_vertical_speed(0.0), "VERTICAL SPEED 0 mm/s")

    def _set_storage_position(self):
        try:
            pos = int(self.storage_pos_var.get())
            self._send(protocol.cmd_storage_position(pos), f"STORAGE POSITION {pos}")
        except ValueError:
            self._log("Invalid position value.")

    def _drill_auto(self):
        try:
            depth = int(self.drill_depth_var.get())
            if not (0 <= depth <= 255):
                self._log("Depth must be between 0 and 255 cm.")
                return
            self._send(protocol.cmd_drill_auto(depth), f"DRILL AUTO depth={depth} cm")
        except ValueError:
            self._log("Invalid depth value.")

    def _stop_auto(self):
        self._send(protocol.cmd_stop_auto(), "STOP AUTO")

    def _store_auto(self):
        self._send(protocol.cmd_store_auto(), "STORE AUTO")

    def _weigh_deep(self):
        self._send(protocol.cmd_weigh_deep(), "WEIGH DEEP")

    def _weigh_surface(self):
        self._send(protocol.cmd_weigh_surface(), "WEIGH SURFACE")

    def _get_weight_deep(self):
        self._send(protocol.cmd_get_weight_deep(), "GET WEIGHT DEEP")

    def _get_weight_surface(self):
        self._send(protocol.cmd_get_weight_surface(), "GET WEIGHT SURFACE")

    def _calibrate_0_deep(self):
        self._send(protocol.cmd_calibrate_0_deep(), "CALIBRATE 0 DEEP")

    def _calibrate_x_deep(self):
        try:
            weight = float(self.calib_weight_var.get())
            self._send(protocol.cmd_calibrate_x_deep(weight), f"CALIBRATE X DEEP ({weight} g)")
        except ValueError:
            self._log("Invalid calibration weight.")

    def _calibrate_0_surface(self):
        self._send(protocol.cmd_calibrate_0_surface(), "CALIBRATE 0 SURFACE")

    def _calibrate_x_surface(self):
        try:
            weight = float(self.calib_weight_var.get())
            self._send(protocol.cmd_calibrate_x_surface(weight), f"CALIBRATE X SURFACE ({weight} g)")
        except ValueError:
            self._log("Invalid calibration weight.")

    def _set_hold_mode(self):
        self._send(protocol.cmd_set_hold_mode(), "SET HOLD MODE")

    def _clear_hold_mode(self):
        self._send(protocol.cmd_clear_hold_mode(), "CLEAR HOLD MODE")

    def _rock_open(self):
        self._send(protocol.cmd_rock_open(), "ROCK OPEN")

    def _rock_close(self):
        self._send(protocol.cmd_rock_close(), "ROCK CLOSE")

    def _sand_open(self):
        self._send(protocol.cmd_sand_open(), "SAND OPEN")

    def _sand_close(self):
        self._send(protocol.cmd_sand_close(), "SAND CLOSE")
