BrnoMarsRover/Drilling/code/mainBoardProgram/src/SurfaceSampleHolder/SurfaceSampleHolder.h

#pragma once

#include <Arduino.h>
#include <HardwareSerial.h>
#include <Wire.h>

#include "../shared/ADS122C04_LIB.h"
#include "servo_mg.h"


class SurfaceSampleHolder
{
public:
  SurfaceSampleHolder(TwoWire& wire, HardwareSerial& debugSerial);
  bool begin();
  
  // -- Servo
  bool openRockBox();
  bool closeRockBox();
  bool openSandBox();
  bool closeSandBox();

  uint8_t getPosRock(); // useless?
  uint8_t getPosSand(); // useless?

  // -- ADC
  bool requestMeasure();
  bool requestTemp();

  bool getResultReady();
  WeightResult getLastWeight();
  float getLastTemp();
  bool getAdcConnected();

  bool setTare();
  bool setCalibration0();
  bool setCalibrationX(float);

private:
  TwoWire& _wire;
  HardwareSerial& _debugSerial;
  ADS122C04 _adcSurface;
  SERVO_MG _servoRock;
  SERVO_MG _servoSand;
};
